ericklein/powered_air_quality/ui/mockups/arc_nox.png

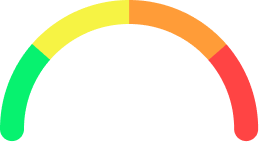
ui/mockups/arc_nox.png
