ericklein/powered_air_quality/post_influx.cpp

/*
  Project:      Powered Air Quality
  Description:  write sensor data to InfluxDB

  See README.md for target information and revision history
*/

#include "Arduino.h"

#include "config.h"               // hardware and internet configuration parameters
#include "powered_air_quality.h"  // overall header info for Powered Air Quality
#include "secrets.h"              // private credentials for network, MQTT, weather provider
#include "data.h"                 // Overall data and metadata naming scheme

// Only compile if InfluxDB enabled
#ifdef INFLUX
  #include <InfluxDbClient.h>

  // Shared helper function
  extern void debugMessage(String messageText, uint8_t messageLevel);

  // Post data to Influx DB using the connection established during setup
  boolean post_influx(float temperatureF, float humidity, uint16_t co2, float pm25, float vocIndex, uint8_t rssi)
  {
    bool success = false;

    // InfluxDB client instance
    String influxURL = "http://" + influxdbConfig.host + ":" + influxdbConfig.port;
    InfluxDBClient dbclient(influxURL, influxdbConfig.org, influxdbConfig.bucket, influxKey);

    // InfluxDB Data point, binds to InfluxDB 'measurement' to use for data. See config.h for value used
    Point dbenvdata(influxdbConfig.envMeasurement);
    Point dbdevdata(influxdbConfig.devMeasurement);
    
    // Add constant Influx data point tags - only do once, will be added to all individual data points
    // Modify if required to reflect your InfluxDB data model (and set values in config.h)
    // First for environmental data
    dbenvdata.addTag(TAG_KEY_DEVICE, hardwareDeviceType);
    dbenvdata.addTag(TAG_KEY_SITE, endpointPath.site);
    dbenvdata.addTag(TAG_KEY_LOCATION, endpointPath.location);
    dbenvdata.addTag(TAG_KEY_ROOM, endpointPath.room);
    dbenvdata.addTag(TAG_KEY_DEVICE_ID, endpointPath.deviceID);
    // And again for device data
    dbdevdata.addTag(TAG_KEY_DEVICE, hardwareDeviceType);
    dbdevdata.addTag(TAG_KEY_SITE, endpointPath.site);
    dbdevdata.addTag(TAG_KEY_LOCATION, endpointPath.location);
    dbdevdata.addTag(TAG_KEY_ROOM, endpointPath.room);
    dbdevdata.addTag(TAG_KEY_DEVICE_ID, endpointPath.deviceID);

    uint32_t timeInfluxConnectStart = millis();
    while ((!dbclient.validateConnection()) && ((millis() - timeInfluxConnectStart) < timeConnectTimeoutSeconds*1000)) {
      delay(100);
    }

    if (dbclient.validateConnection()) {
      // Connected, so store sensor values into timeseries data points
      debugMessage(String("Connected to InfluxDB: ") + dbclient.getServerUrl(),2);

      dbenvdata.clearFields();
      // Report sensor readings
      dbenvdata.addField(VALUE_KEY_PM25, pm25);
      dbenvdata.addField(VALUE_KEY_TEMPERATURE, temperatureF);
      dbenvdata.addField(VALUE_KEY_HUMIDITY, humidity);
      dbenvdata.addField(VALUE_KEY_VOC, vocIndex);
      dbenvdata.addField(VALUE_KEY_CO2, co2);
      // Write point to InfluxDB host
      if (dbclient.writePoint(dbenvdata)) {
        debugMessage(String("InfluxDB environment update success"), 1);
        debugMessage(String("Return message: ") + dbclient.pointToLineProtocol(dbenvdata), 2);
        success = true;
      }
      else { 
        debugMessage(String("InfluxDB environment update failed"), 1);
        debugMessage(String("InfluxDB environment update error msg: ") + dbclient.getLastErrorMessage(), 2);
      }
      // Now store device information 
      dbdevdata.clearFields();
      // Report device readings
      dbdevdata.addField(VALUE_KEY_RSSI, rssi);
      // Write point via connection to InfluxDB host
      if (dbclient.writePoint(dbdevdata)) {
        debugMessage(String("InfluxDB device update success"), 1);
        debugMessage(String("Return message: ") + dbclient.pointToLineProtocol(dbdevdata), 2);
        success = true;
      }
      else {
        debugMessage(String("InfluxDB device update failed"), 1);
        debugMessage(String("InfluxDB device update update error msg: ") + dbclient.getLastErrorMessage(), 2);
      }
      dbclient.flushBuffer();  // Clear pending writes
    }
    else {
      debugMessage("Could not connect to influxdb server",1);
    }
    return (success);
  }
#endif
