ericklein/powered_air_quality/data.h

/*
  Project:      Powered Air Quality
  Description:  data pair configuration
*/

#ifndef DATA_H
  #define DATA_H

  // Define tag keys used to store important device attributes in
  // InfluxDB.  Will be used as InfluxDB tag keys for the associated attribute.

  #define TAG_KEY_SITE       "site"       // maps to endpointPath.site in powered_air_quality.h
  #define TAG_KEY_LOCATION   "location"   // maps to endpointPath.location in powered_air_quality.h
  #define TAG_KEY_ROOM       "room"       // maps to endpointPath.room in powered_air_quality.h
  #define TAG_KEY_DEVICE     "device"     // maps to hardwareDeviceType in config.h
  #define TAG_KEY_DEVICE_ID  "device_id"  // maps to endpointPath.deviceID in powered_air_quality.h

  // Defines value keys (strings) used for representing stored 
  // sensor and device data as key/value pairs in InfluxDB and
  // as parts of MQTT topics.  Must be unique, and must conform
  // to syntax required for field keys by InfluxDB and MQTT.

  #define VALUE_KEY_TEMPERATURE   "tempF"
  #define VALUE_KEY_HUMIDITY      "humidity"
  #define VALUE_KEY_CO2           "co2"
  // #define VALUE_KEY_PRESSURE   "pressure"
  #define VALUE_KEY_PM25          "pm25"
  #define VALUE_KEY_AQI           "aqi"
  #define VALUE_KEY_VOC           "vocIndex"
  #define VALUE_KEY_RSSI          "rssi"

#endif  // #ifdef DATA_H
